mpvano/radiohat2/libradiohat/GRC/NewTransceiver/ssb_mod.pdf

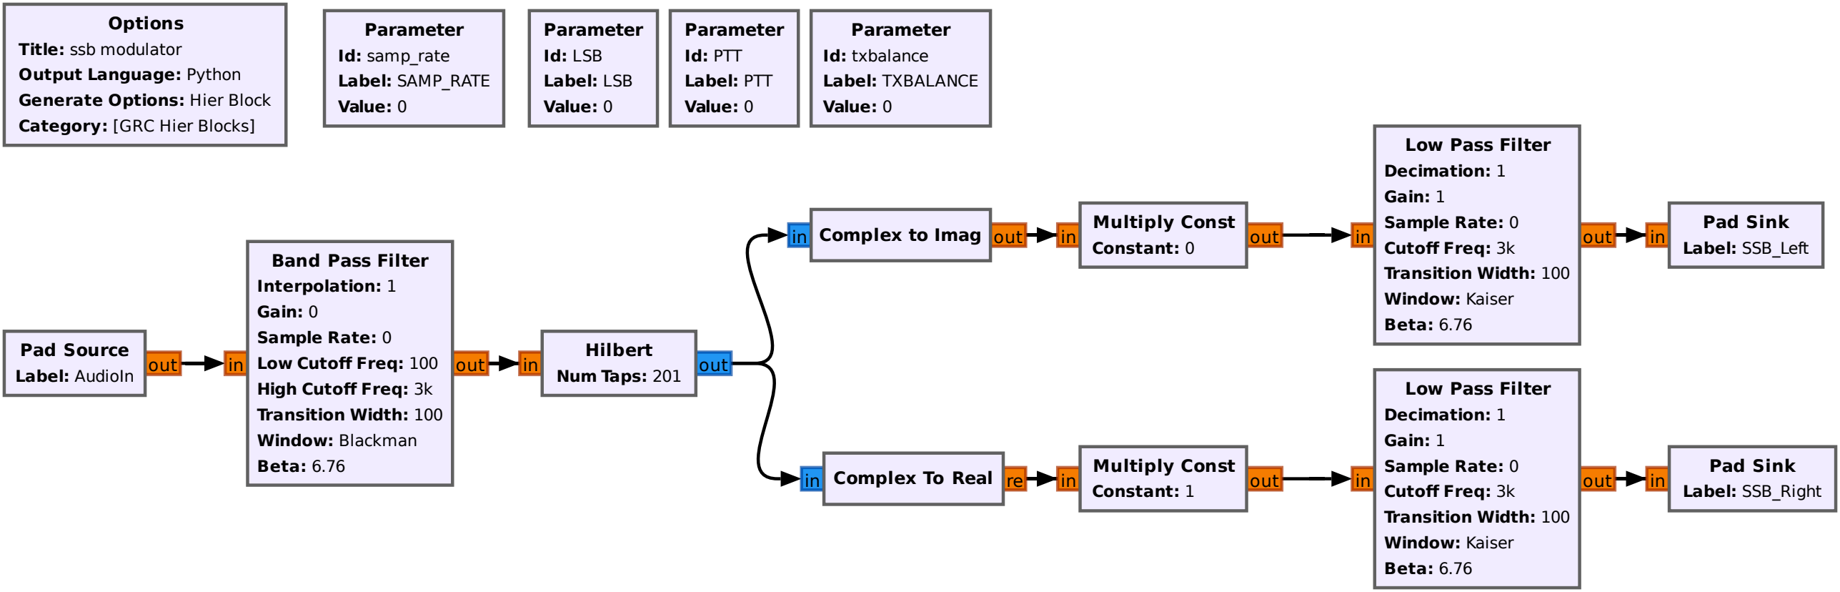
[picture p2: figure]
Options Title: ssb modulator Output Language: Python Generate Options: Hier Block Category: [GRC Hier Blocks]; Parameter Id: LSB Label: LSB Value: 0; Parameter Id: PTT Label: PTT Value: 0; out; Band Pass Filter Interpolation: 1 Gain: 0 Sample Rate: 0 Low Cutoff Freq: 100 High Cutoff Freq: 3k Transition Width: 100 Window: Blackman Beta: 6.76; Complex to Imag; Complex To Real; out Multiply Const; Constant: 1; Constant: 0; Hilbert Num Taps: 201; Low Pass Filter Decimation: 1 Gain: 1 Sample Rate: 0 Cutoff Freq: 3k Transition Width: 100 Window: Kaiser Beta: 6.76; Pad Sink Label: SSB_Left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
