mpvano/radiohat2/libradiohat/GRC/NewTransceiver/ssb_demod.pdf

Options
Title: ssb_demodulator
Output Language: Python
Generate Options: Hier Block Category: [GRC Hier Blocks]

Parameter
Id: LSB
Label: LSB_SWITCH
Value: 0

Parameter
Id: samp_rate
Label: SAMP_RATE
Value: 0

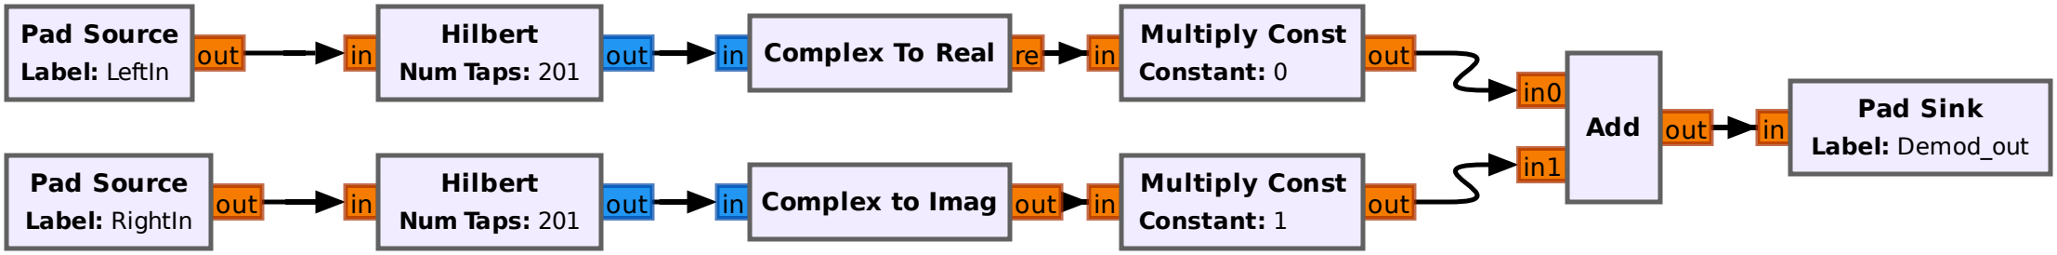
[picture p4: figure]
out; Add; Complex to Imag; Complex To Real; out Multiply Const; Constant: 0; Constant: 1 in; Hilbert Num Taps: 201; Pad Sink Label: Demod_out; Pad Source Label: LeftIn; Pad Source Label: RightIn
