mpvano/radiohat2/FAB/txfilters1/datasheets/Stockton bridge/swrpwr2.jpg

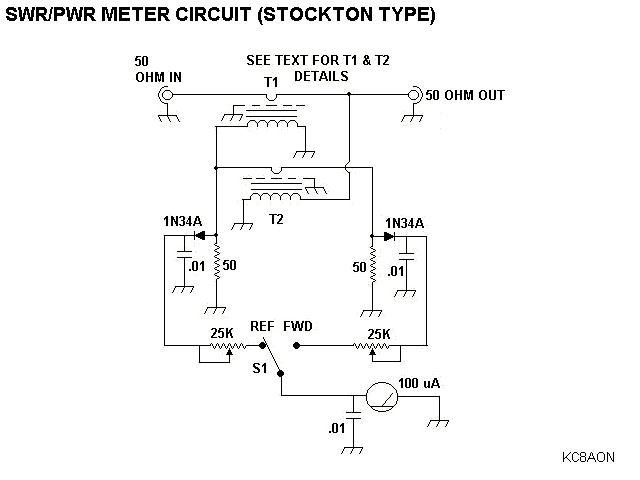
FAB/txfilters1/datasheets/Stockton bridge/swrpwr2.jpg
