mpvano/radiohat2/FAB/txfilters1/datasheets/Stockton bridge/Tandem match, two transformers.png

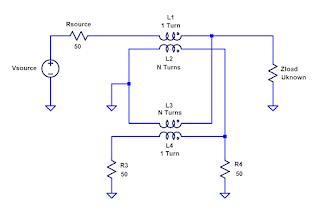
FAB/txfilters1/datasheets/Stockton bridge/Tandem match, two transformers.png
