mpvano/radiohat2/FAB/radiohat2_QFP32/Seeed/BOM Template.xlsx

Designator | Manufacturer Part Number or Seeed SKU | Qty | Link
C1,C2,C3,C4,C5 | RHA0J471MCN1GS | 5 | https://www.digikey.com.cn/product-detail/zh/nichicon/RHA0J471MCN1GS/493-3771-1-ND/2209480
A1,A4 | RH0111-30002 | 2 | https://statics3.seeedstudio.com/images/opl/datasheet/318020010.pdf
D1 | CYBLE-014008-00 | 1 | https://www.digikey.com.cn/product-detail/zh/cypress-semiconductor-corp/CYBLE-014008-00/428-3600-1-ND/6052585
