mpvano/radiohat2/docs/install.jpg

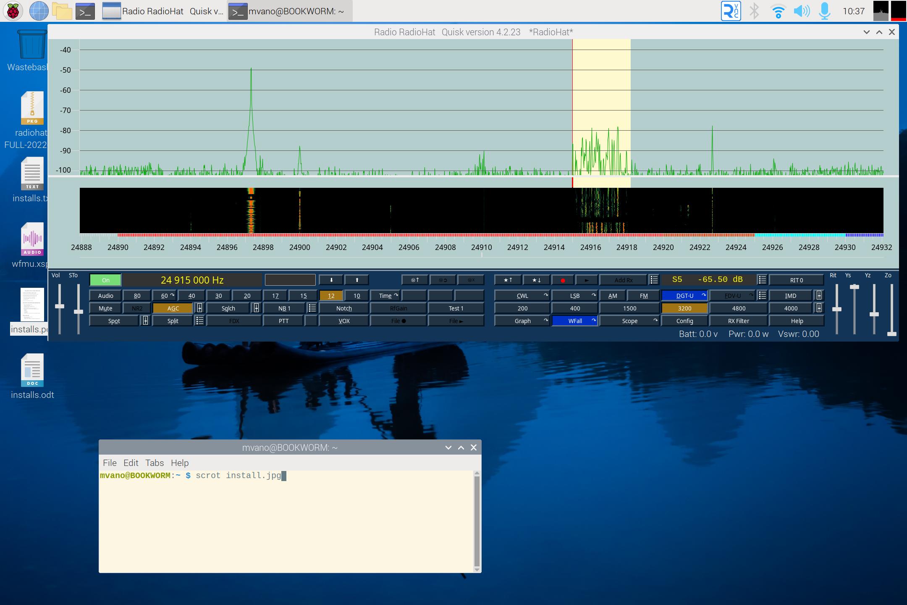
docs/install.jpg
