mpvano/radiohat2/FAB/radiohat2_QFP32/PCBA/radiohead.pdf

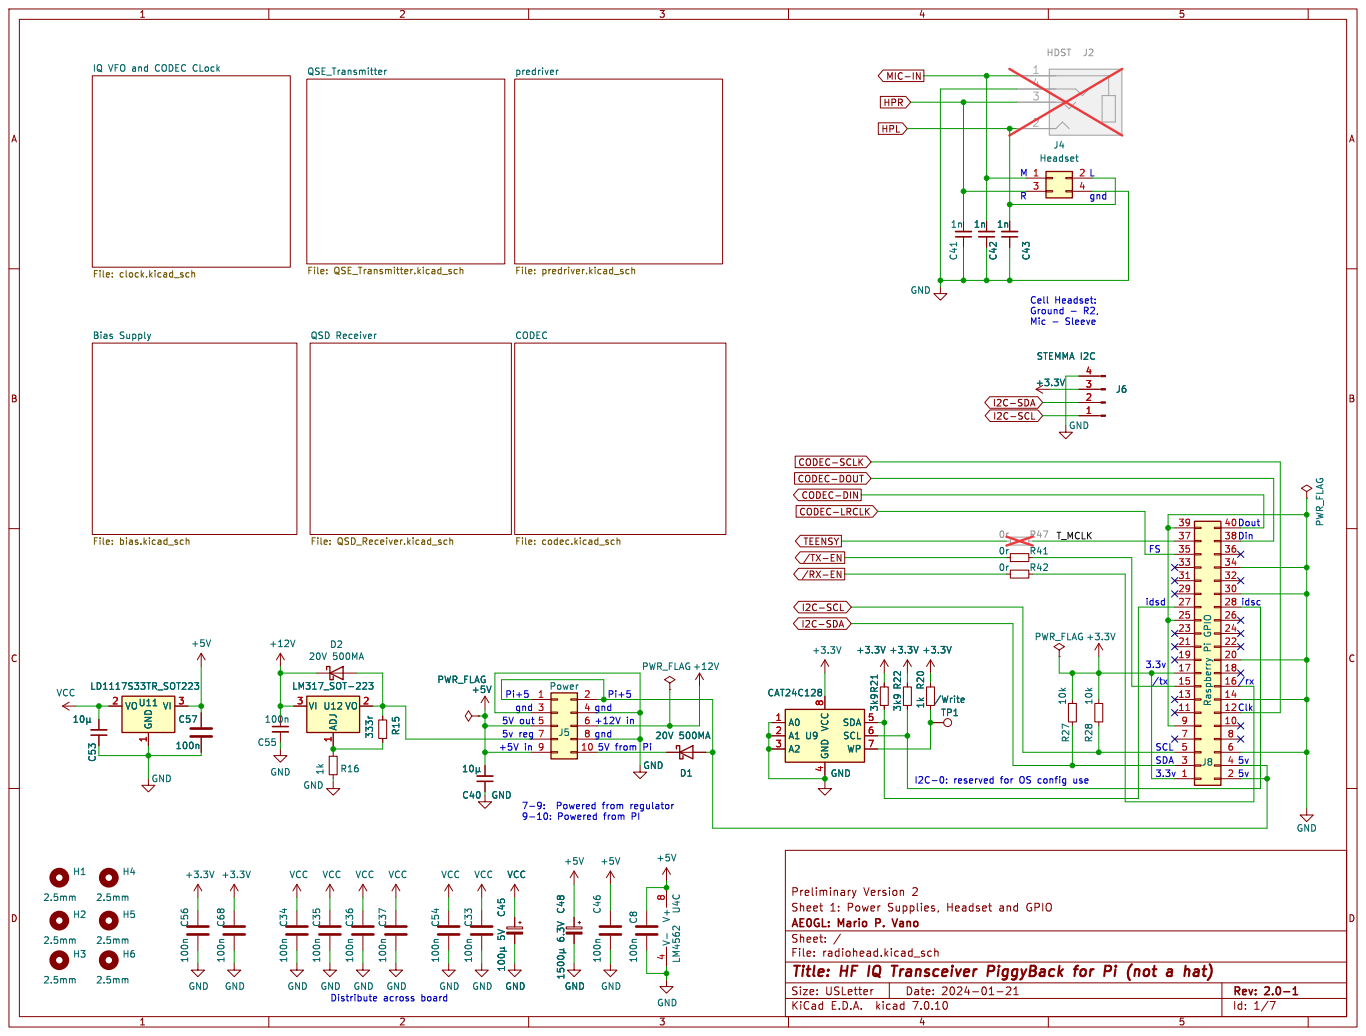
[picture p44: page 1]

4 HDST J2
J4 Headset 1
I2C-SDA HPL MIC-IN

IQ VFO and CODEC CLock File: clock.kicad_sch

idsc Cell Headset: Ground - R2, Mic - Sleeve

8 U9 CAT24C128 R21 3k9 +3.3V GND ADJ 1 VO 2 VI 3 U12

CODEC-DOUT CODEC-SCLK CODEC-DIN

4 SDA 5 SCL 6 WP 7 VCC

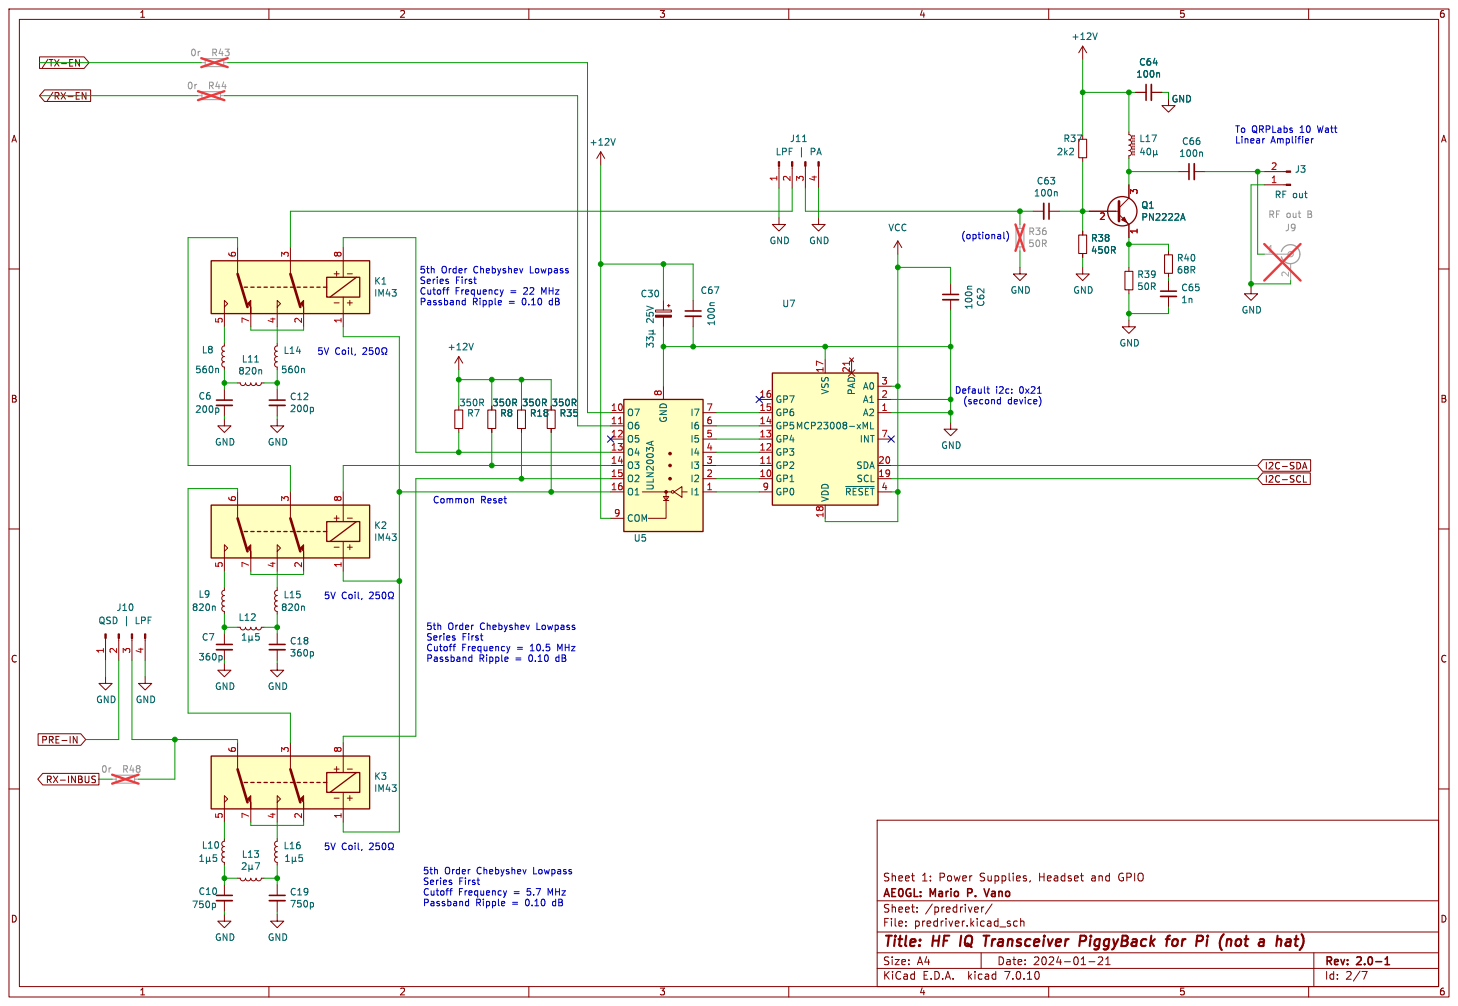
[picture p45: page 2]

5th Order Chebyshev Lowpass Series First Cutoff Frequency = 22 MHz Passband Ripple = 0.10 dB

5th Order Chebyshev Lowpass Series First Cutoff Frequency = 10.5 MHz Passband Ripple = 0.10 dB R18

Common Reset 5V Coil, þÿ250©

5th Order Chebyshev Lowpass Series First Cutoff Frequency = 5.7 MHz Passband Ripple = 0.10 dB

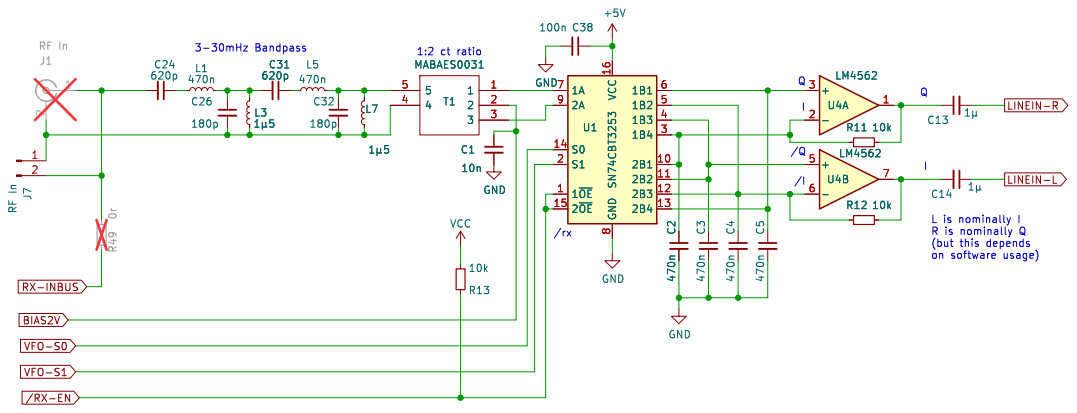
[picture p46: page 3]

(but this depends on software usage)

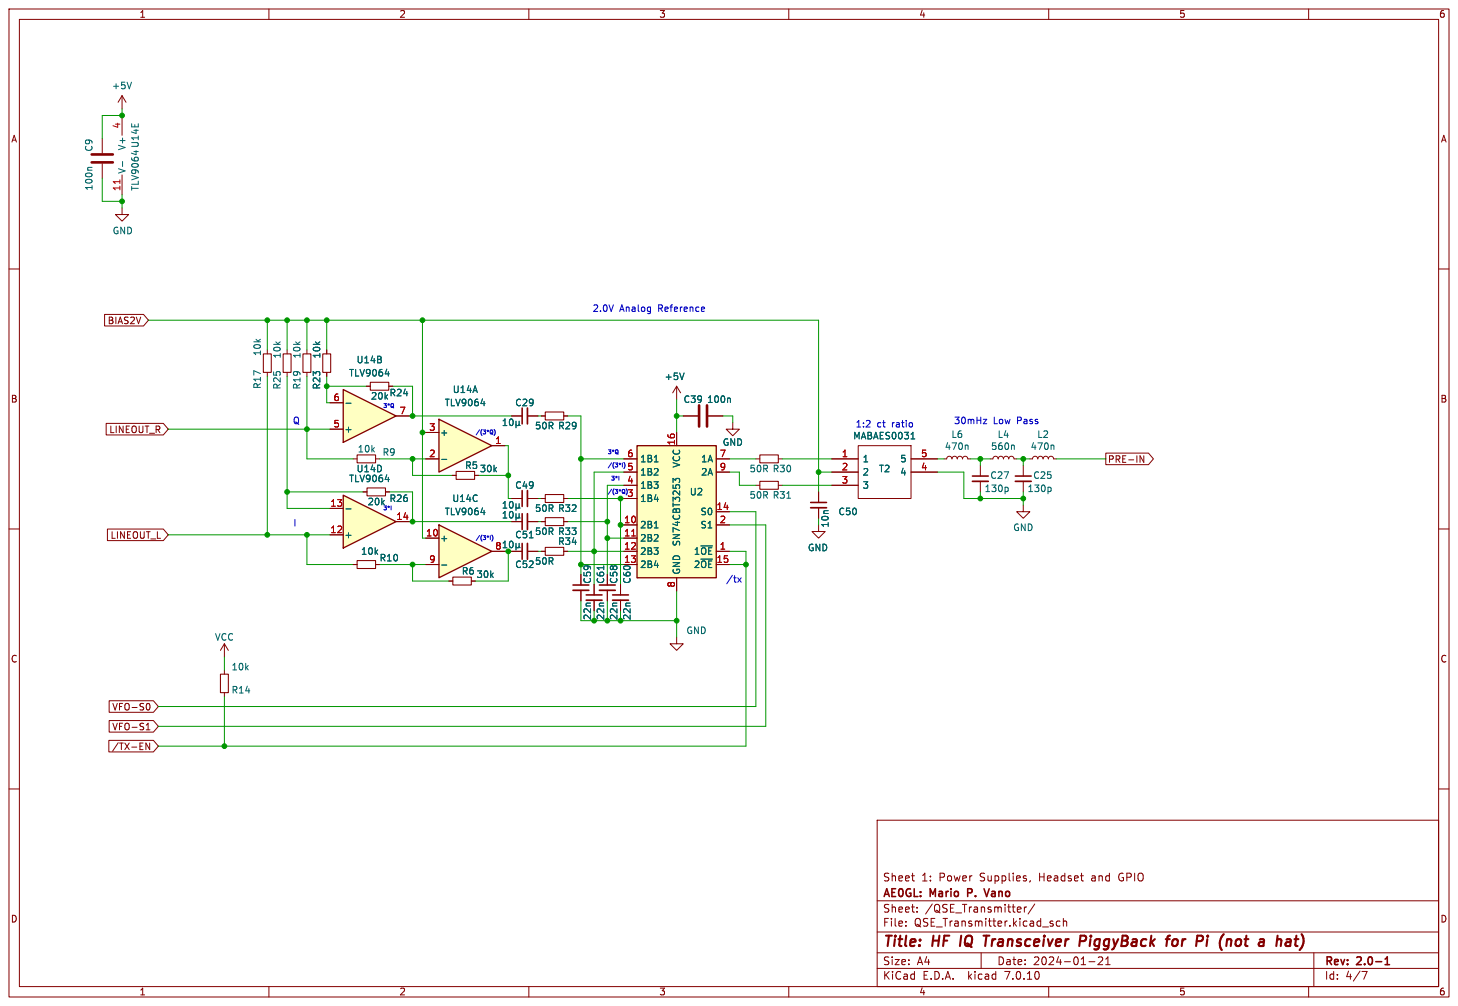
[picture p47: page 4]

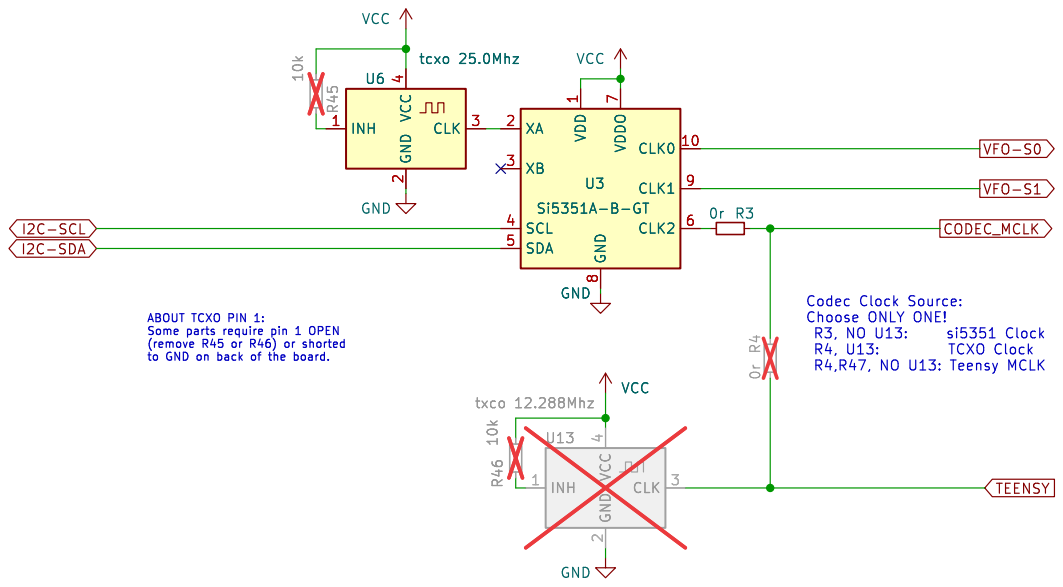
[picture p48: page 5]

1 CLK0 10 XA 2 XB 3 SCL 4 SDA 5 CLK2 6 VDDO

ABOUT TCXO PIN 1: Some parts require pin 1 OPEN

(remove R45 or R46) or shorted


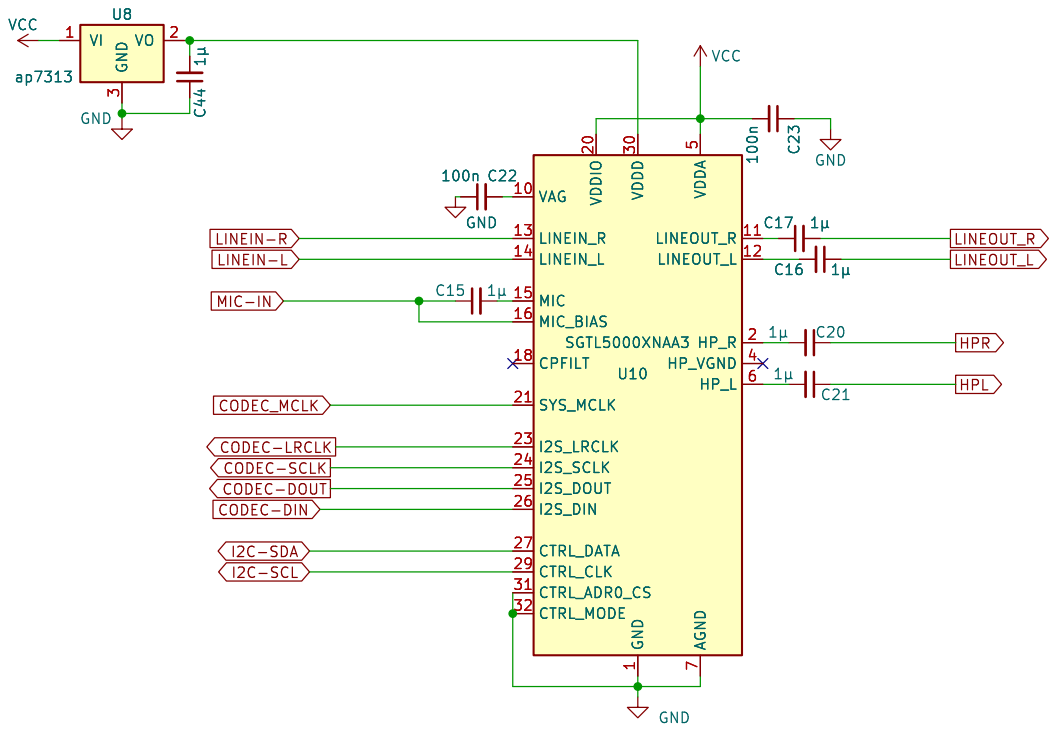
[picture p49: page 7]

I2C-SDA CODEC-LRCLK CODEC-DOUT U8
