mpvano/radiohat2/libradiohat/GRC/NewTransceiver/transceiver.pdf

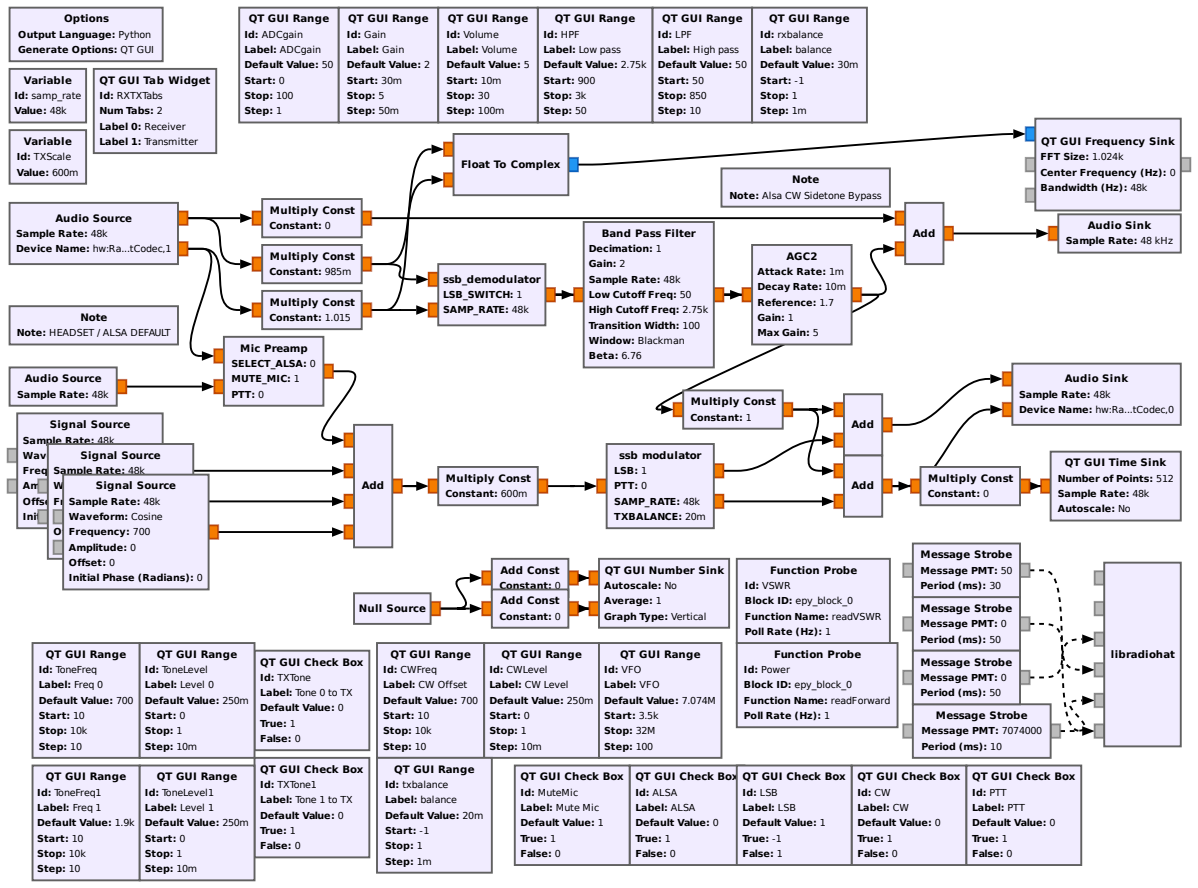
[picture p50: page 1]
Options; Variable Id: TXScale Value: 600m; Variable Id: samp_rate Value: 48k; AGC2 Attack Rate: 1m Decay Rate: 10m Reference: 1.7 Gain: 1 Max Gain: 5; Signal Source Sample Rate: 48k Waveform: Cosine Frequency: 1.9k Amplitude: 0; Signal Source Sample Rate: 48k Waveform: Cosine Frequency: 700 Amplitude: 0; Audio Sink; Audio Source; Audio Source Sample Rate: 48k; Add Const Constant: 0 Add Const Constant: 0; Add; Message Strobe Message PMT: 7074000 Period (ms): 10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

QT GUI Range
Id: ADCgain
Label: ADCgain
Default Value: 50
Start: 0
Stop: 100
Step: 1

Id: Gain
Label: Gain
Default Value: 2
Start: 30m
Stop: 5
Step: 50m

Id: Volume
Label: Volume
Default Value: 5
Start: 10m
Stop: 30
Step: 100m

Id: HPF
Label: Low pass
Default Value: 2.75k
Start: 900
Stop: 3k
Step: 50

Id: LPF
Label: High pass
Start: 50
Stop: 850
Step: 10

Id: rxbalance
Label: balance
Default Value: 30m
Start: -1
Stop: 1
Step: 1m

Output Language: Python
Generate Options: QT GUI

QT GUI Tab Widget
Id: RXTXTabs
Num Tabs: 2
Label 0: Receiver
Label 1: Transmitter

QT GUI Frequency Sink
FFT Size: 1.024k
Center Frequency (Hz): 0
Bandwidth (Hz): 48k

Float To Complex

Note: Alsa CW Sidetone Bypass

Audio Sink
Sample Rate: 48 kHz

Sample Rate: 48k
Device Name: hw:Ra...tCodec,1

Band Pass Filter
Decimation: 1
Gain: 2
Low Cutoff Freq: 50
High Cutoff Freq: 2.75k
Transition Width: 100
Window: Blackman
Beta: 6.76

Note: HEADSET / ALSA DEFAULT

Device Name: hw:Ra...tCodec,0

Signal Source
Waveform: Cosine
Frequency: 700
Amplitude: 0
Offset: 0
Initial Phase (Radians): 0

QT GUI Time Sink
Number of Points: 512
Autoscale: No

QT GUI Number Sink
Average: 1
Graph Type: Vertical

Function Probe
Id: VSWR
Block ID: epy_block_0
Function Name: readVSWR
Poll Rate (Hz): 1
Id: Power
Function Name: readForward

Id: ToneFreq
Label: Freq 0
Default Value: 700
Start: 10
Stop: 10k

Id: ToneLevel
Label: Level 0
Default Value: 250m
Step: 10m

Id: CWFreq
Label: CW Offset
Id: txbalance
Default Value: 20m

Id: CWLevel
Label: CW Level

Id: VFO
Label: VFO
Default Value: 7.074M
Start: 3.5k
Stop: 32M
Step: 100

QT GUI Check Box
Id: TXTone
Label: Tone 0 to TX
Default Value: 0
True: 1
False: 0

Id: TXTone1
Label: Tone 1 to TX

Id: ToneFreq1
Label: Freq 1
Default Value: 1.9k

Id: ToneLevel1
Label: Level 1

Id: MuteMic
Label: Mute Mic
Default Value: 1

Id: ALSA
Label: ALSA

Id: LSB
Label: LSB
True: -1
False: 1

Label: CW

Id: PTT
Label: PTT
