mpvano/radiohat2/FAB/radiohat2_QFP32/PCBA/FabPlot.pdf

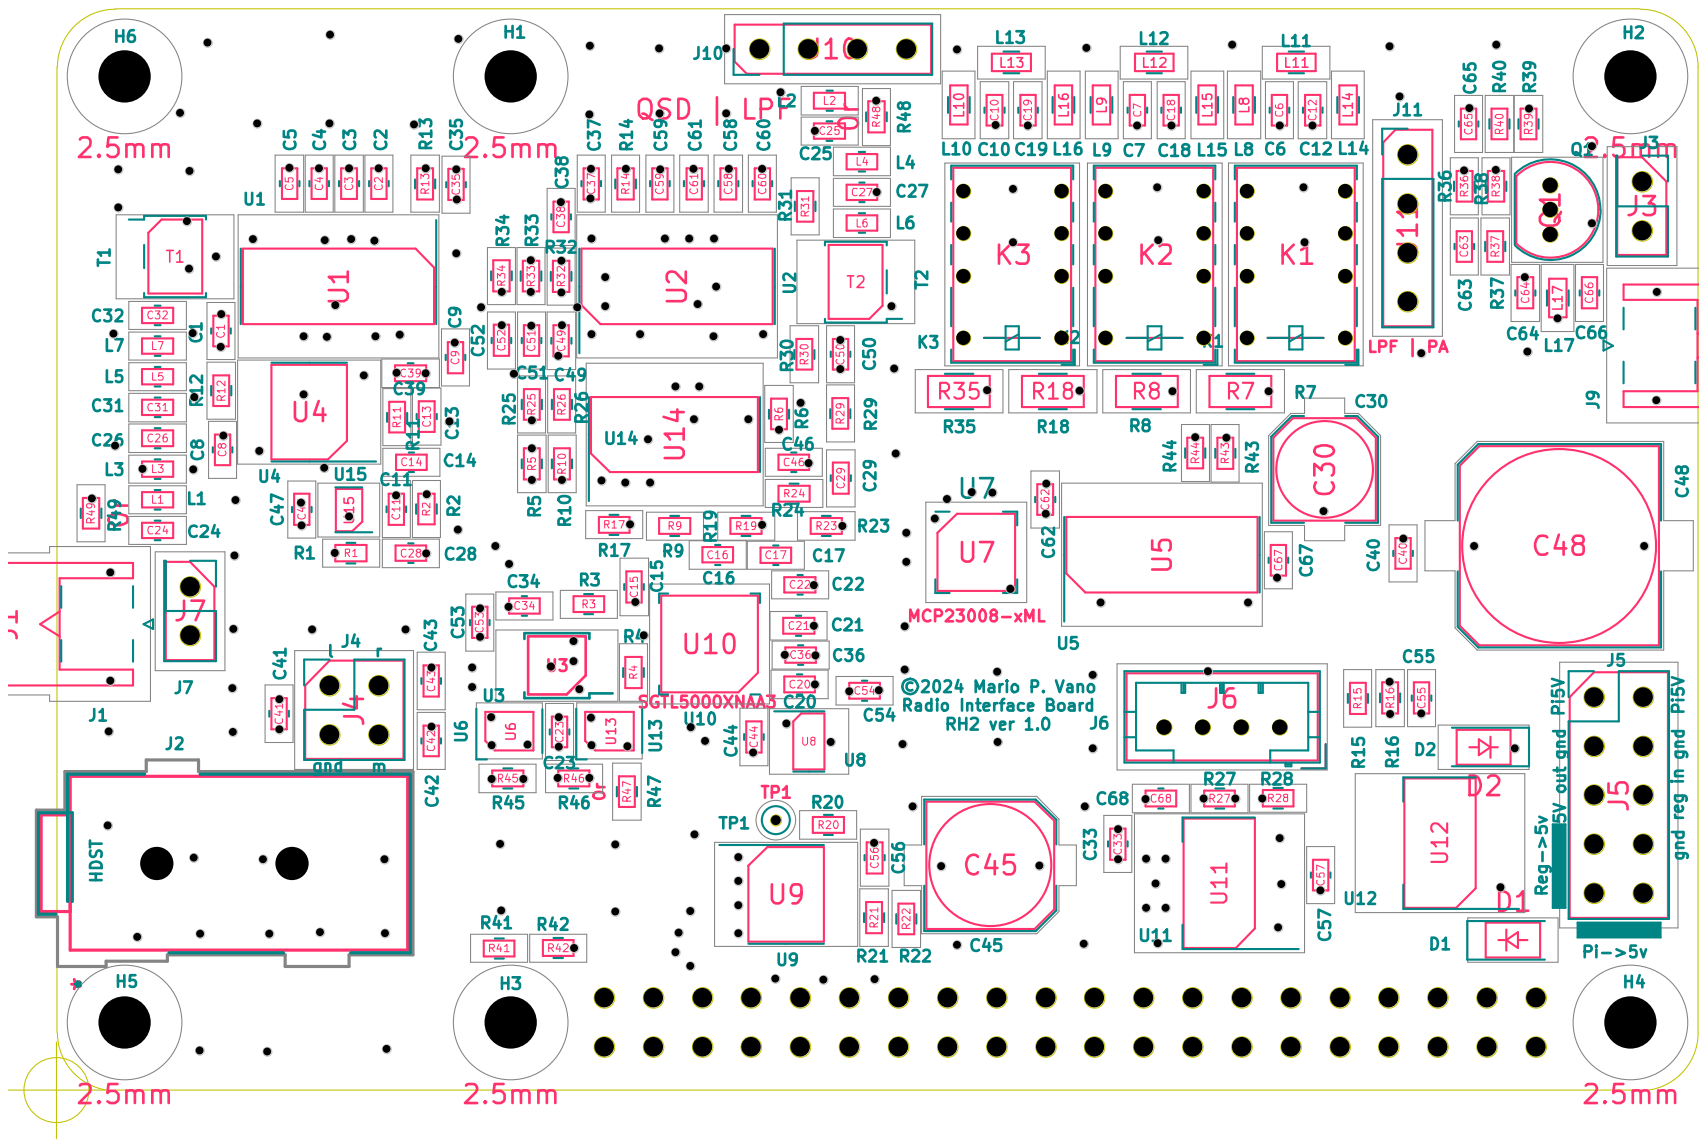
[picture p52: page 1]
