mpvano/radiohat2/FAB/radiohat2/PCBA/FABDrawing.pdf

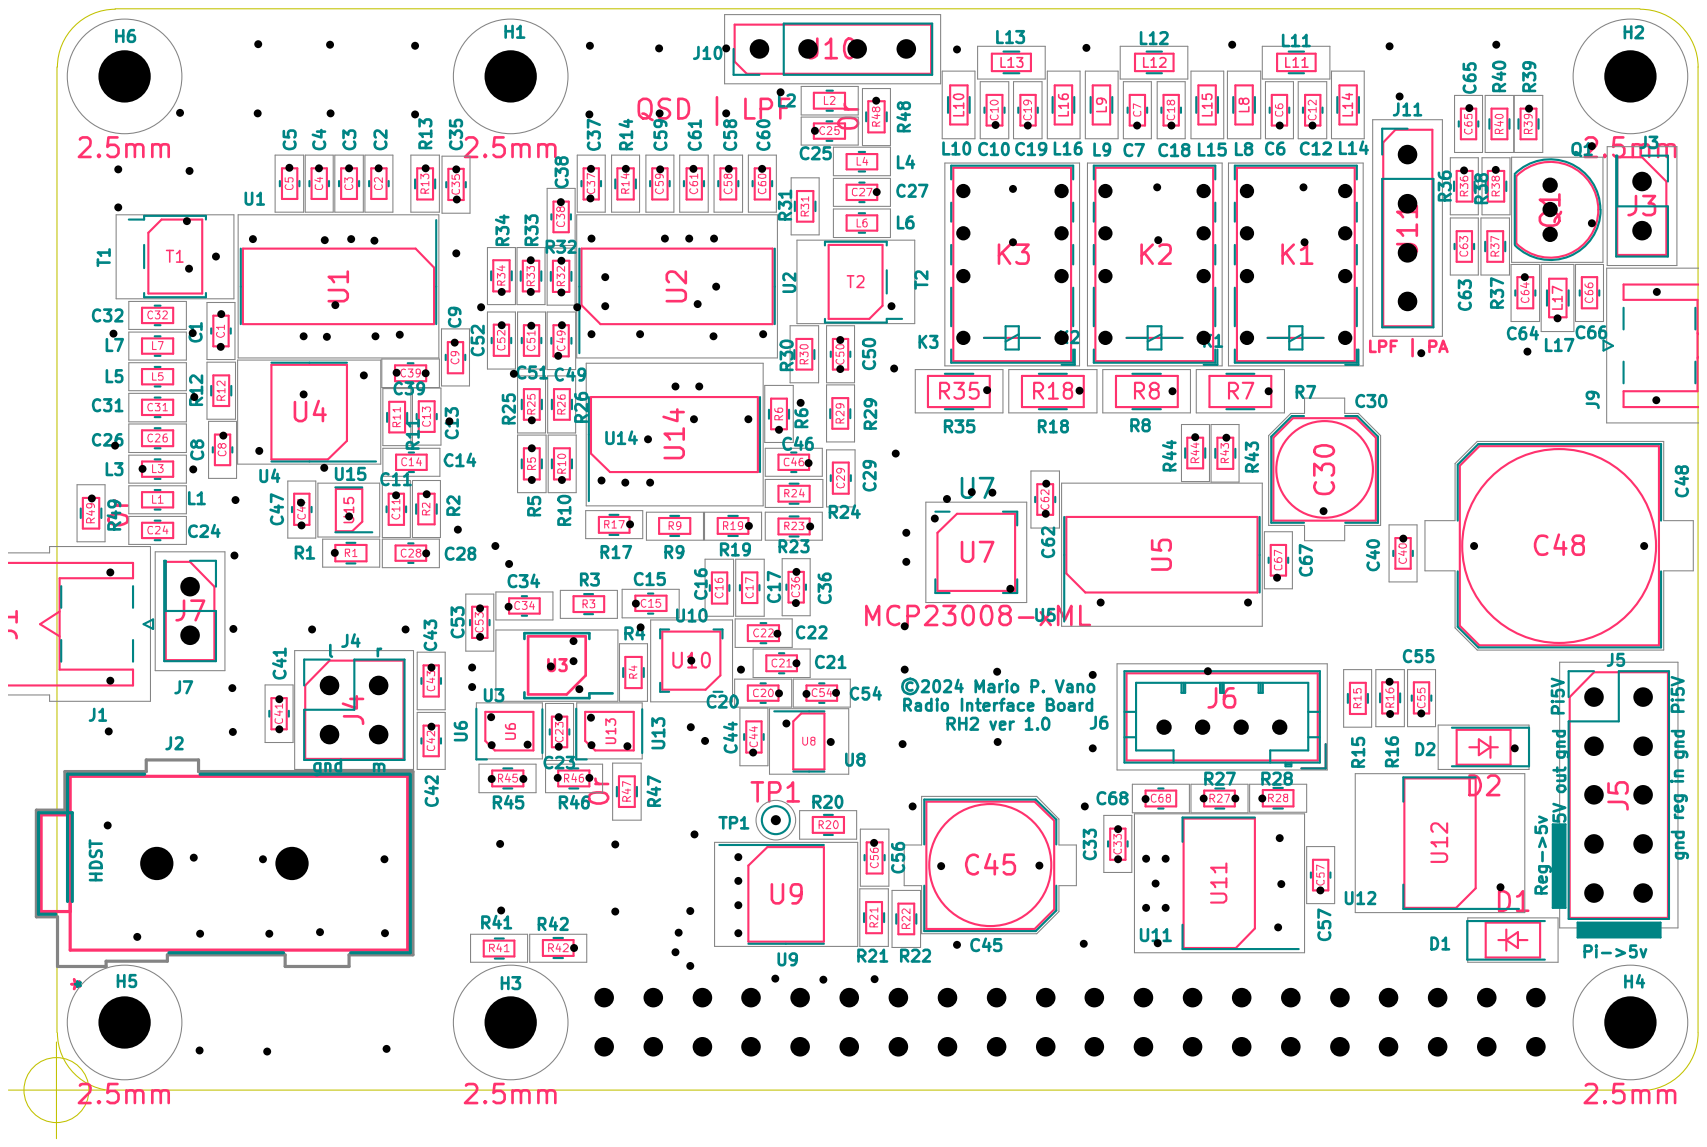
[picture p53: page 1]
