mpvano/radiohat2/FAB/txfilters1/5bandFilters/40M.asc

C1: cap; 270p
C3: cap; 680p
C5: cap; 680p
C7: cap; 270p
L2: ind; 1.38µ; Rser=1
L4: ind; 1.70µ; Rser=1
L6: ind; 1.38µ; Rser=1
RL: res; 50
V1: voltage; ""; AC 1 0; Rser=50.00
Named nets: 0
.ac dec 1001 5.0Meg 50.00Meg
.net I(RL) V1
7th Order Chebyshev Lowpass
Shunt First
Cutoff Frequency = 4.0 MHz
Passband Ripple = 0.10 dB

rf-tools.com | Feb 21 2024 16:04
Inductor Q Factor = 30 at 14.50MHz
