mpvano/radiohat2/libradiohat/GRC/headset/MuteIfNotRX.py

"""
Embedded Python Blocks:

Each time this file is saved, GRC will instantiate the first class it finds
to get ports and parameters of your block. The arguments to __init__  will
be the parameters. All of them are required to have default values!
"""

import numpy as np
from gnuradio import gr
from gpiozero import Button
import RPi.GPIO as GPIO


class blk(gr.sync_block):  # other base classes are basic_block, decim_block, interp_block
    """Embedded Python Block example - a simple multiply const"""


    def __init__(self, example_param=22):  # only default arguments here
        """arguments to this function show up as parameters in GRC"""
        gr.sync_block.__init__(
            self,
            name='Embedded Python Block',   # will show up in GRC
            in_sig=[np.float32],
            out_sig=[np.float32]
        )
        # if an attribute with the same name as a parameter is found,
        # a callback is registered (properties work, too).
        self.example_param = example_param
        GPIO.setwarnings(False)
        GPIO.setmode(GPIO.BCM)
        GPIO.setup(self.example_param, GPIO.OUT)


    def work(self, input_items, output_items):
        """example: multiply with constant"""
#        output_items[0][:] = input_items[0] * self.example_param
        if GPIO.input(self.example_param):
            output_items[0][:] = 0
        else:
            output_items[0][:] = input_items[0] * 1.0
        return len(output_items[0])
